LabibProjects/Bangladesh_Team-Electrobot/Mobility Management/Chasis/bearing placement.png

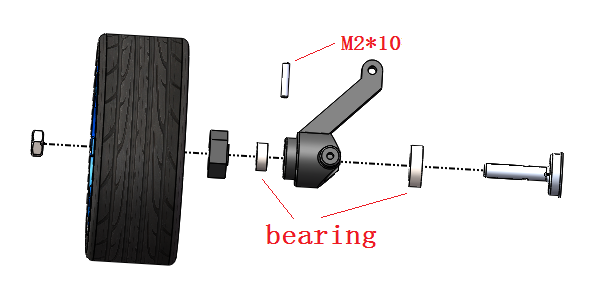
Mobility Management/Chasis/bearing placement.png
