LabibProjects/Bangladesh_Team-Electrobot/Mobility Management/Chasis/Front axel.png

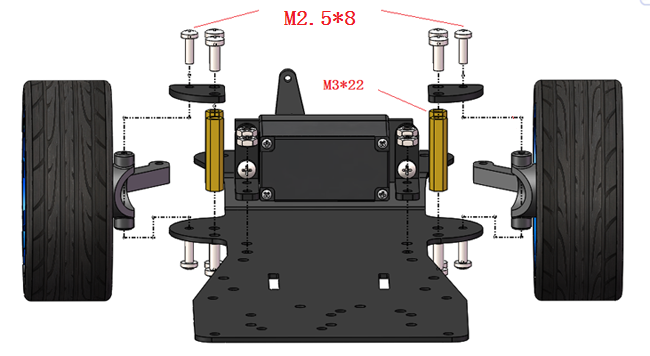
Mobility Management/Chasis/Front axel.png
