LabibProjects/Bangladesh_Team-Electrobot/Mobility Management/Chasis/main motor .png

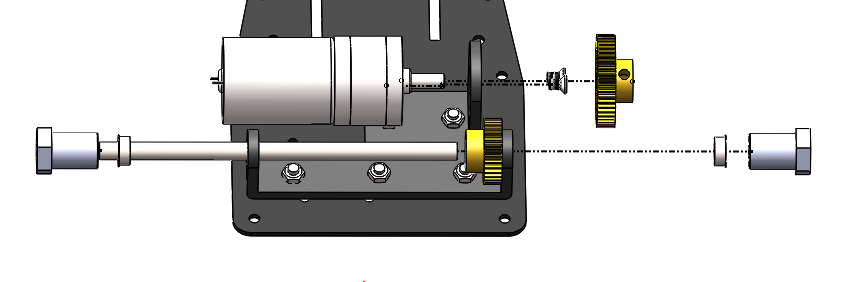
Mobility Management/Chasis/main motor .png
