LabibProjects/Bangladesh_Team-Electrobot/Mobility Management/Chasis/Servo placement.png

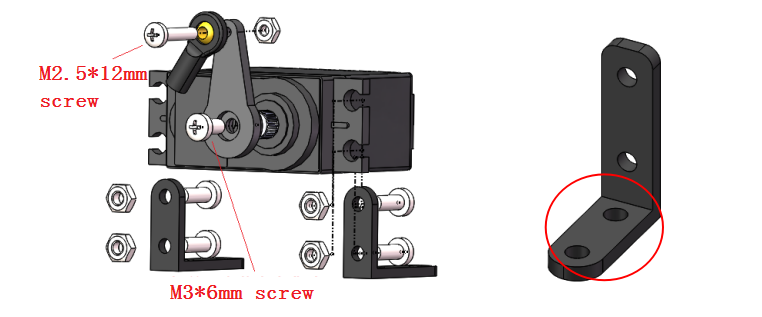
Mobility Management/Chasis/Servo placement.png
