LabibProjects/Bangladesh_Team-Electrobot/schemes/Block_Diagram.jpeg

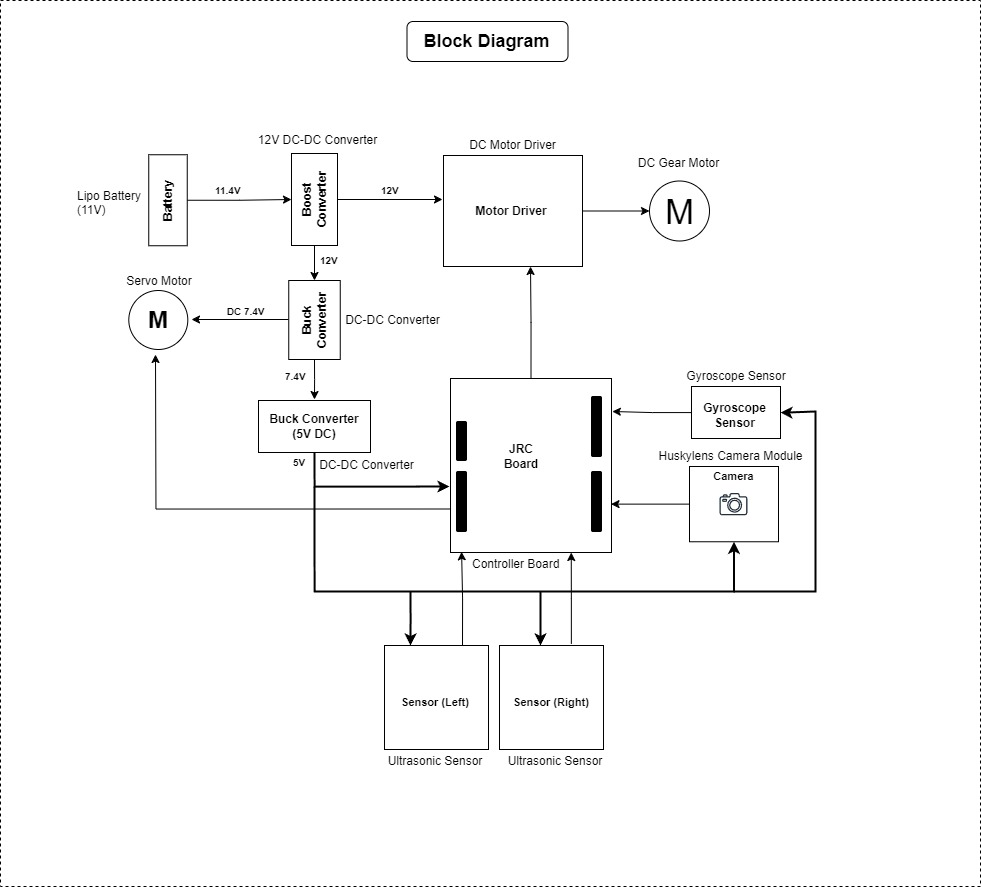
schemes/Block_Diagram.jpeg
