LabibProjects/Bangladesh_Team-Electrobot/schemes/PCB_3d_model.jpeg

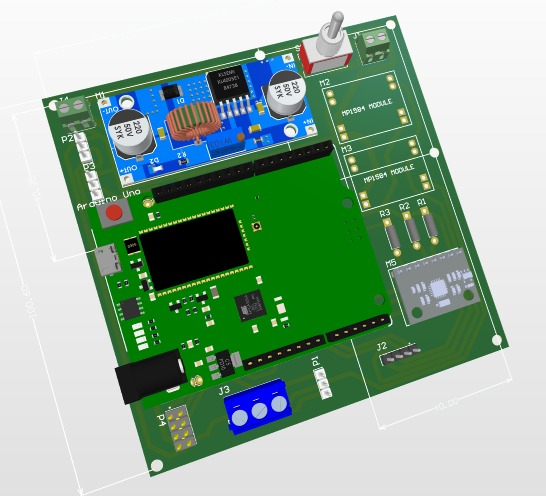
schemes/PCB_3d_model.jpeg
