LabibProjects/Bangladesh_Team-Electrobot/schemes/System_management.jpeg

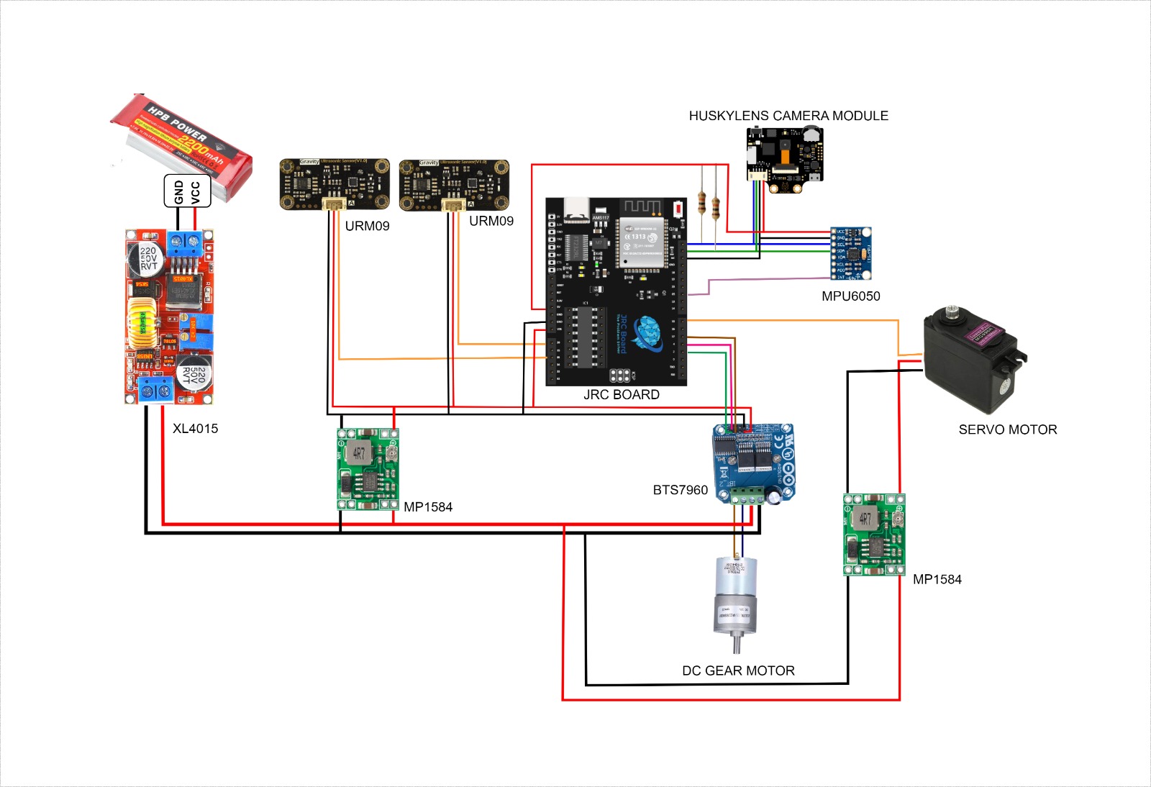
schemes/System_management.jpeg
