LabibProjects/Bangladesh_Team-Electrobot/v-photos/bottom.jpeg

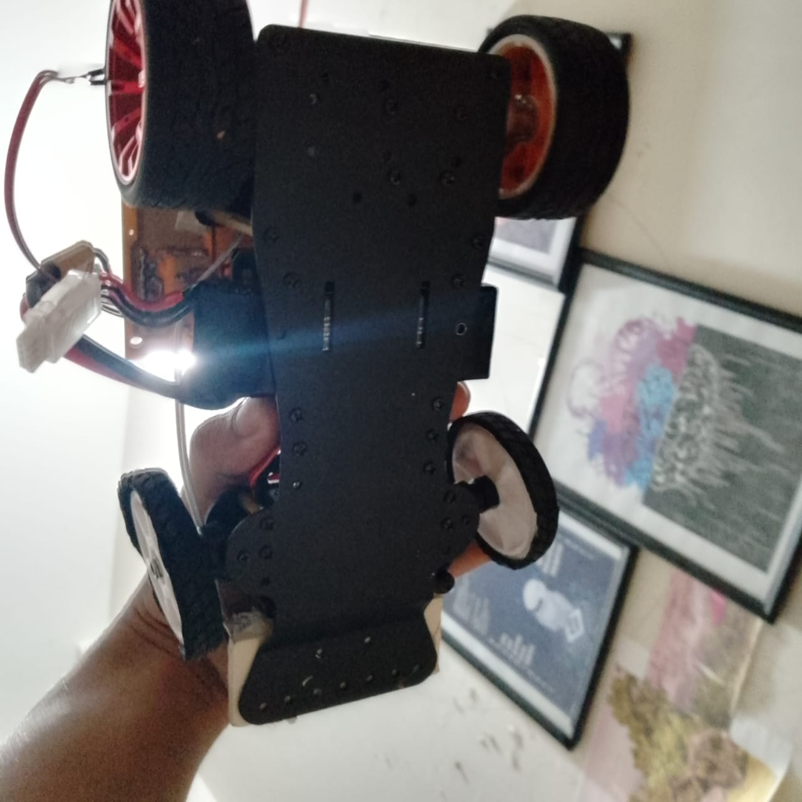
v-photos/bottom.jpeg
