LabibProjects/Bangladesh_Team-Electrobot/v-photos/top.jpeg

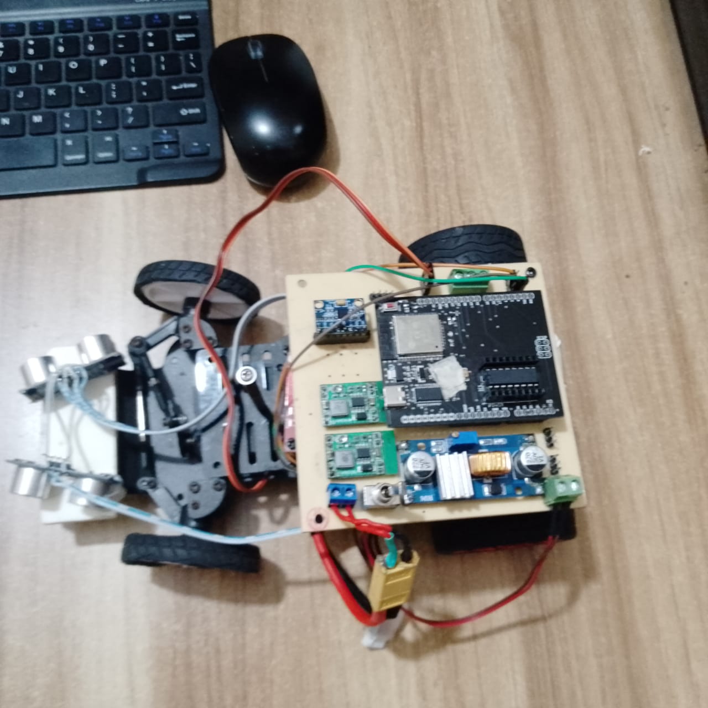
v-photos/top.jpeg
